InnoGreenTech/CO2-DHT22-ESP-sensor/CapteurCO2_oled_128x32/send_data.ino

void send_data(){


    
    if ( WiFi.status()!= WL_CONNECTED)
    
        {
          return;
        /*if (nb_cycle_lost_wifi<NB_TRYING_CONNECT)                            // test the wifi connection  if lost it, reset the module
                      {
                      nb_cycle_lost_wifi++;
                      lastmessage = lastmessage+30000;
                      return;              
                      } 

        else {ESP.reset();}  // if the lost of wifi*/
        }
      

      String ip=WiFi.localIP().toString().c_str();
      String data;

      const size_t bufferSize =JSON_OBJECT_SIZE(7);
     // DynamicJsonBuffer jsonBuffer(bufferSize);
     DynamicJsonDocument root(bufferSize);
                  
                  
      //JsonObject& root = jsonBuffer.createObject();
      root["mac_adress"]=WiFi.macAddress();
      root["ip_adress"]=ip; 
      root["p1"] =  co2;
      root["p2"] =  temperature;
      root["p3"]=   humidity;
      serializeJson(root,data);
      //Serial.println(data);

     //root.printTo(data);
     String adresse="http://";
     //adresse+="www.home.innogreentech.fr";
     adresse+=ip_server;
     adresse+="/InnoGreenTech/controller/json_probe.php";
     String data1= "data=";
     data1 +=data;
     //Serial.println(data1);

     HTTPClient http;
     int httpCode = 0;
     http.begin(adresse);
     http.addHeader("Content-Type", "application/x-www-form-urlencoded"); //http.addHeader("Content-Type", "application/json");
     httpCode = http.POST(data1);
     String payload = http.getString();
     //Serial.println(httpCode);   //Print HTTP return code
     //Serial.println(payload);
     http.end();  //Close connection
      
      /* Création des données json */      
      nb_cycle_lost_wifi=0;      
      lastmessage= millis();
  
}
